rhit-bennetev/quad-rx/ControllerFirmware/data/images/3SP_Mouthpiece.png

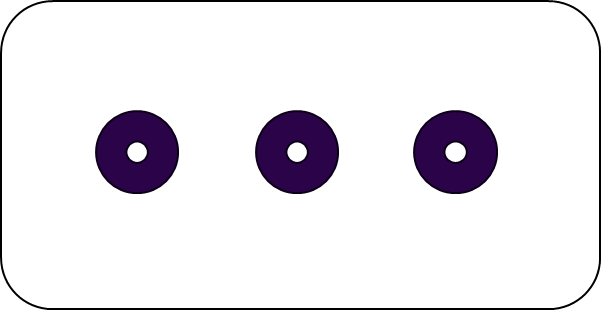
ControllerFirmware/data/images/3SP_Mouthpiece.png
