rhit-bennetev/quad-rx/ControllerFirmware/data/images/playstation-controller.png

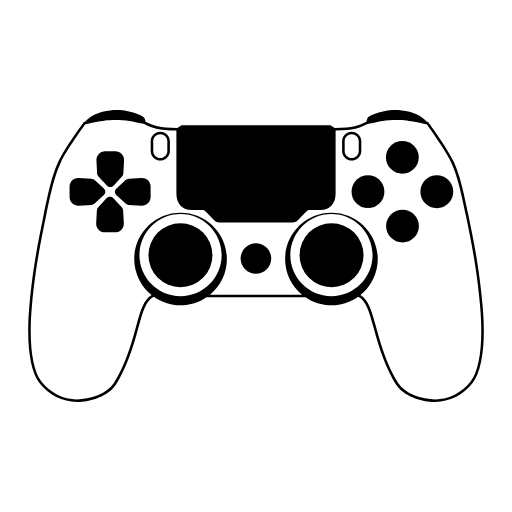
ControllerFirmware/data/images/playstation-controller.png
