rhit-bennetev/quad-rx/ControllerFirmware/data/images/switch-controller.png

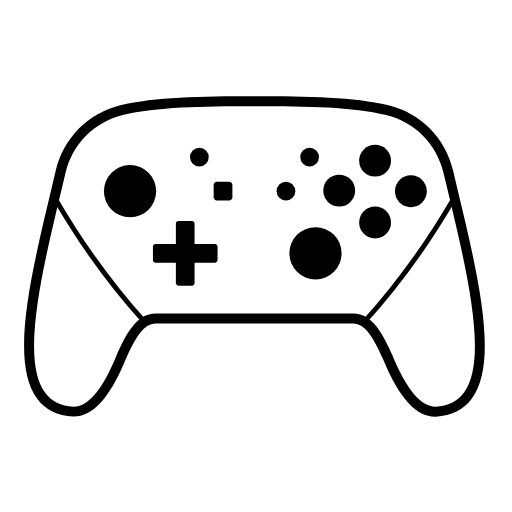
ControllerFirmware/data/images/switch-controller.png
